limingjie/CH32V003-Segment-LCD/Schematic/CH32V003 3-Digit Segment LCD Driver/CH32V003 3-Digit Segment LCD Driver.kicad_sch

## KiCad design Schematic/CH32V003 3-Digit Segment LCD Driver/CH32V003 3-Digit Segment LCD Driver.kicad_sch (2025-10-08)

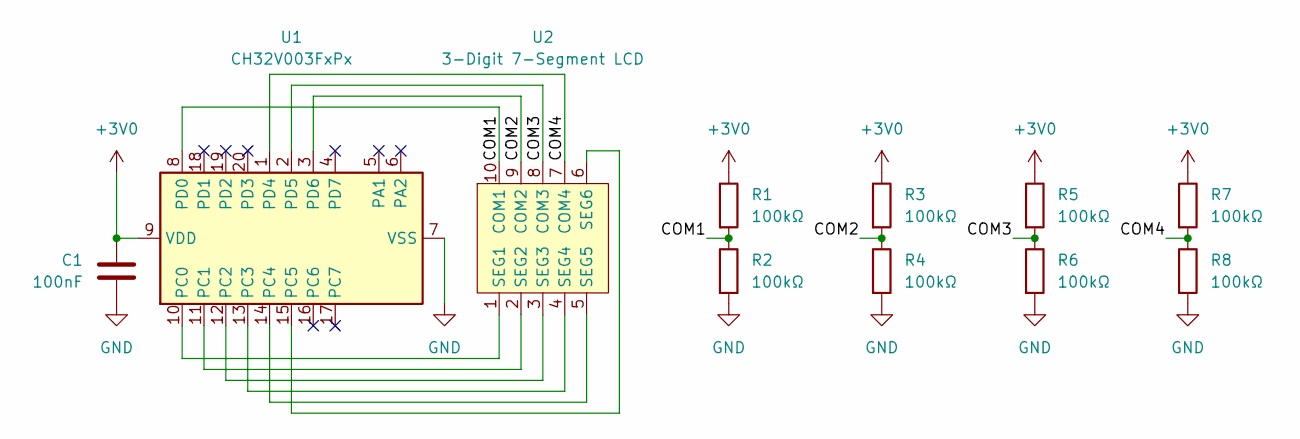
[picture p11: schematic CH32V003 3-Digit Segment LCD Driver.kicad_sch]

Parts:
C1: 100nF
R1, R2, R3, R4, R5, R6, R7, R8: 100kΩ
U1: CH32V003FxPx; TSSOP-20_4.4x6.5mm_P0.65mm
U2: 3-Digit 7-Segment LCD

Connections:
+3V0: C1.1, R1.1, R3.1, R5.1, R7.1, U1.9 (VDD)
COM1: R1.2, R2.1, U1.8 (PD0), U2.10 (COM1)
COM2: R3.2, R4.1, U1.3 (PD6), U2.9 (COM2)
COM3: R5.2, R6.1, U1.2 (PD5), U2.8 (COM3)
COM4: R7.2, R8.1, U1.1 (PD4), U2.7 (COM4)
GND: C1.2, R2.2, R4.2, R6.2, R8.2, U1.7 (VSS)
unnamed: U1.10 (PC0), U2.1 (SEG1)
unnamed: U1.11 (PC1), U2.2 (SEG2)
unnamed: U1.12 (PC2), U2.3 (SEG3)
unnamed: U1.13 (PC3), U2.4 (SEG4)
unnamed: U1.14 (PC4), U2.5 (SEG5)
unnamed: U1.15 (PC5), U2.6 (SEG6)
